urbanlab/Maison-Miniature/CAHIER DE PLANS/MOBILIER/IMPRESSION 3D/SDB-Baignoire.stl

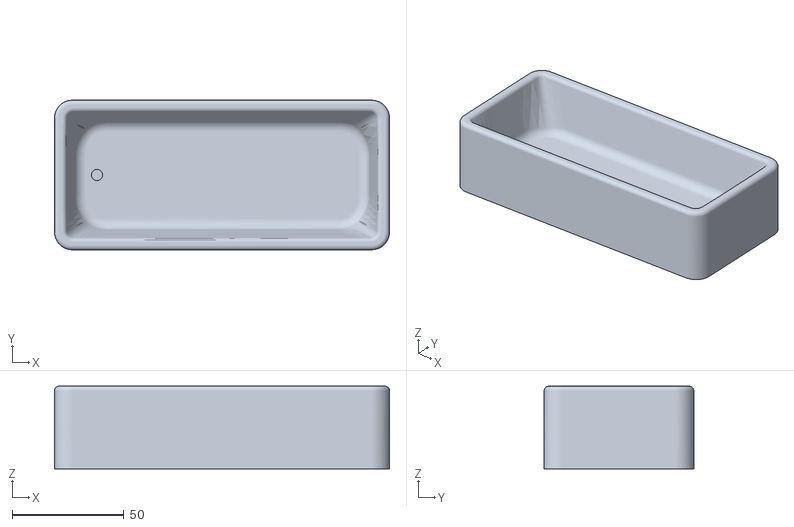
[picture p19: CAD file, 2018-12-10]
CAHIER DE PLANS/MOBILIER/IMPRESSION 3D/SDB-Baignoire.stl
150.0 x 67.0 x 37.0
