urbanlab/Maison-Miniature/CAHIER DE PLANS/MOBILIER/IMPRESSION 3D/SAL-Plafonnier support X2.stl

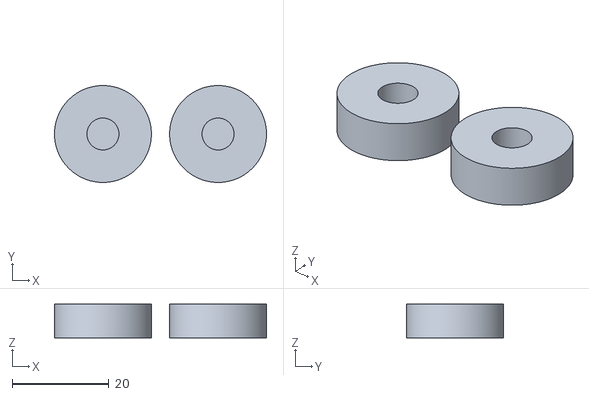
[picture p20: CAD file, 2018-12-10]
CAHIER DE PLANS/MOBILIER/IMPRESSION 3D/SAL-Plafonnier support X2.stl
43.8 x 20.0 x 7.00
