urbanlab/Maison-Miniature/CAHIER DE PLANS/MOBILIER/IMPRESSION 3D/CUIS-Four.stl

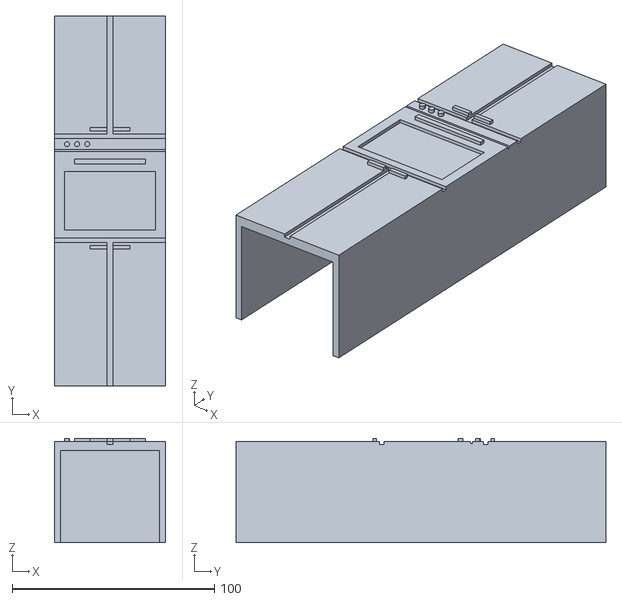
[picture p21: CAD file, 2018-12-10]
CAHIER DE PLANS/MOBILIER/IMPRESSION 3D/CUIS-Four.stl
55.0 x 183.0 x 51.5
