urbanlab/Maison-Miniature/CAHIER DE PLANS/MOBILIER/IMPRESSION 3D/CUIS-Frigo.stl

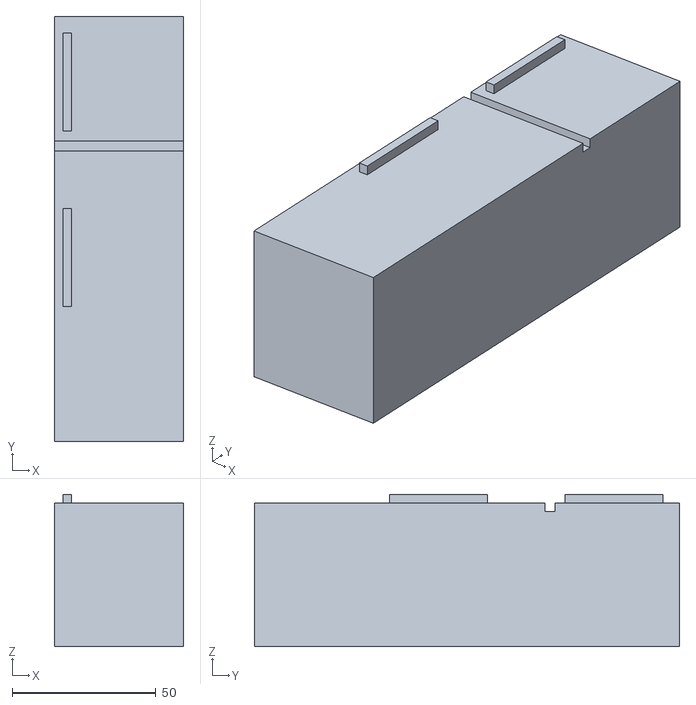
[picture p22: CAD file, 2018-12-10]
CAHIER DE PLANS/MOBILIER/IMPRESSION 3D/CUIS-Frigo.stl
45.0 x 148.0 x 53.0
