urbanlab/Maison-Miniature/CAHIER DE PLANS/MOBILIER/IMPRESSION 3D/SAL-Lampe basse.stl

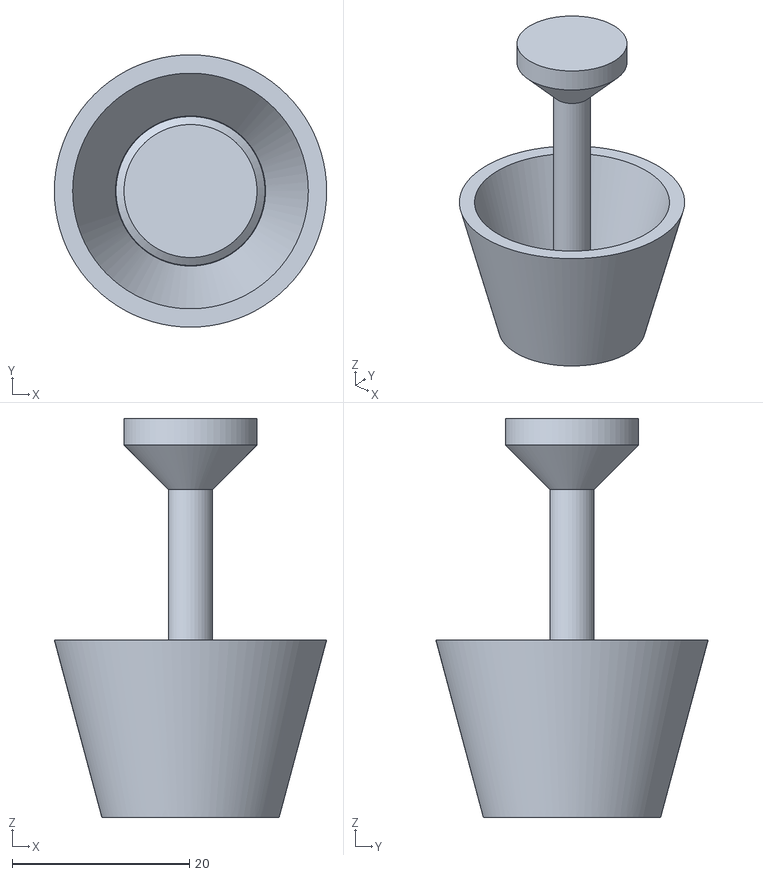
[picture p23: CAD file, 2018-12-10]
CAHIER DE PLANS/MOBILIER/IMPRESSION 3D/SAL-Lampe basse.stl
30.7 x 30.7 x 45.0
