urbanlab/Maison-Miniature/CAHIER DE PLANS/MOBILIER/IMPRESSION 3D/OUV_Porte cuisine.stl

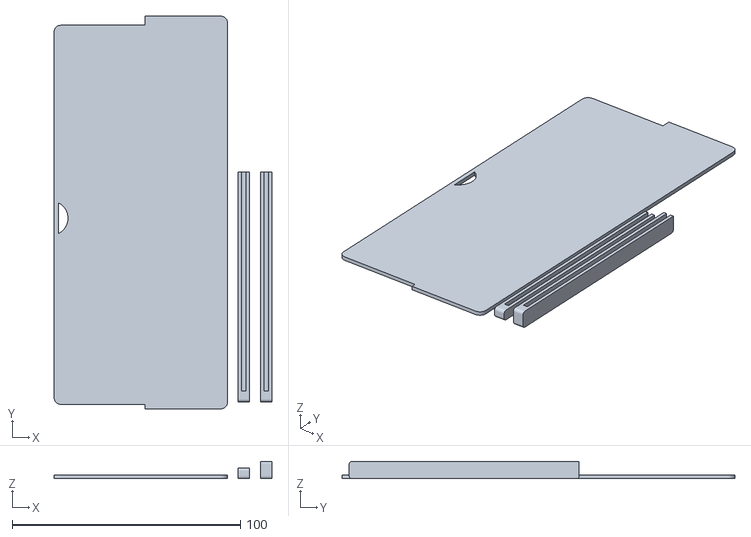
[picture p24: CAD file, 2018-12-10]
CAHIER DE PLANS/MOBILIER/IMPRESSION 3D/OUV_Porte cuisine.stl
95.4 x 172.0 x 7.60
