urbanlab/Maison-Miniature/CAHIER DE PLANS/MOBILIER/IMPRESSION 3D/CUIS-Chaise accoudoire X2.stl

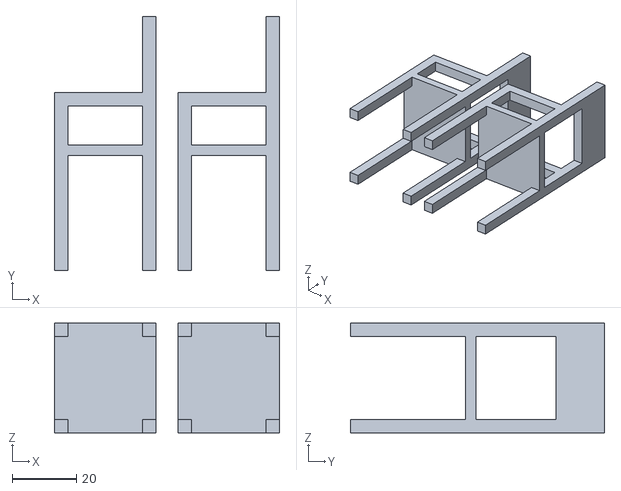
[picture p25: CAD file, 2018-12-10]
CAHIER DE PLANS/MOBILIER/IMPRESSION 3D/CUIS-Chaise accoudoire X2.stl
70.1 x 79.2 x 34.2
