urbanlab/Maison-Miniature/CAHIER DE PLANS/MOBILIER/IMPRESSION 3D/SAL-Fauteuil rehausse.stl

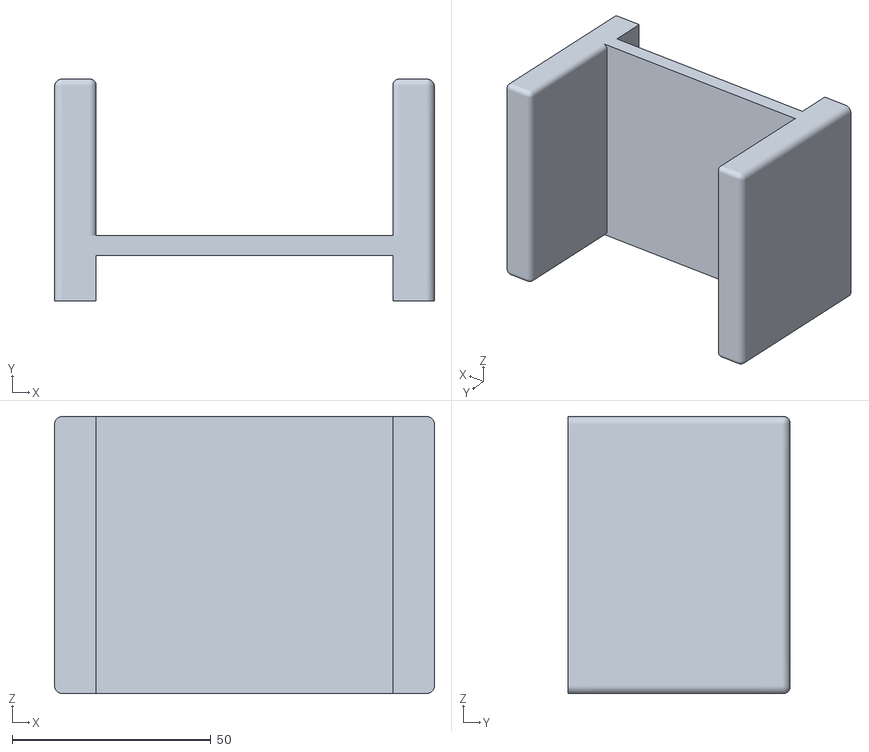
[picture p26: CAD file, 2018-12-10]
CAHIER DE PLANS/MOBILIER/IMPRESSION 3D/SAL-Fauteuil rehausse.stl
95.6 x 55.9 x 69.7
