urbanlab/Maison-Miniature/CAHIER DE PLANS/MOBILIER/IMPRESSION 3D/CUIS-Bloc Vitro.stl

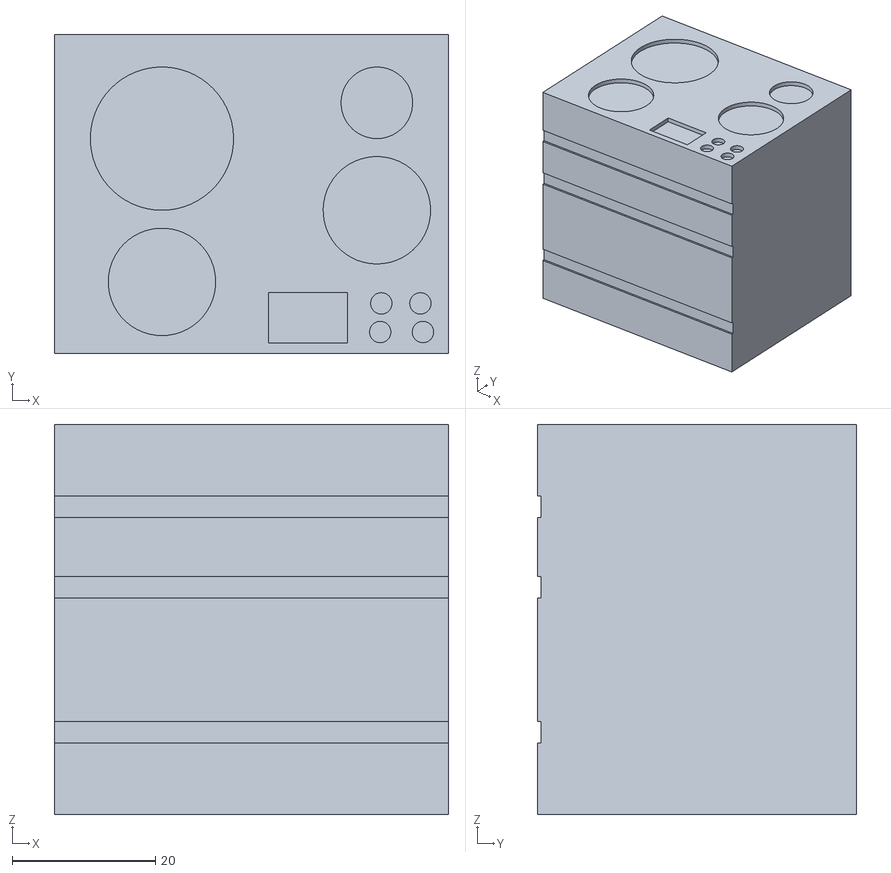
[picture p27: CAD file, 2018-12-10]
CAHIER DE PLANS/MOBILIER/IMPRESSION 3D/CUIS-Bloc Vitro.stl
55.0 x 44.5 x 54.5
