urbanlab/Maison-Miniature/CAHIER DE PLANS/MOBILIER/IMPRESSION 3D/SDB-Lavabo.stl

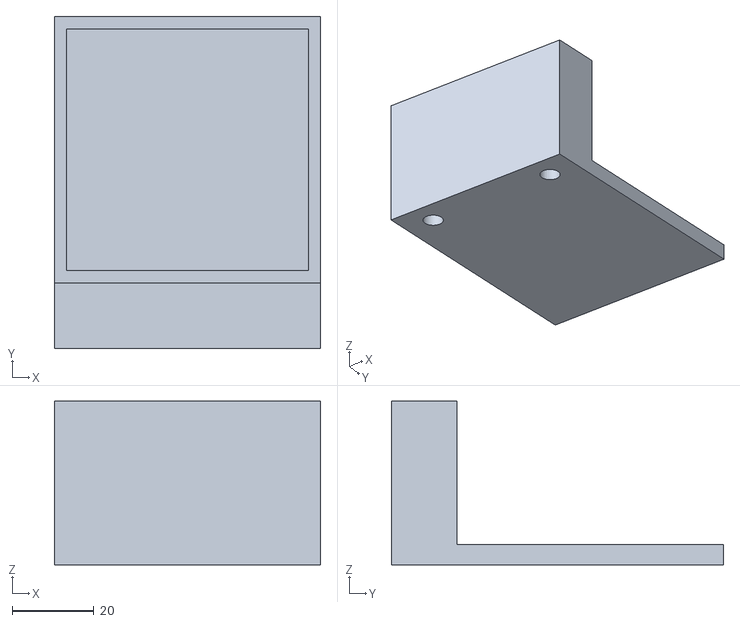
[picture p28: CAD file, 2018-12-10]
CAHIER DE PLANS/MOBILIER/IMPRESSION 3D/SDB-Lavabo.stl
65.0 x 81.0 x 40.0
