urbanlab/Maison-Miniature/CAHIER DE PLANS/MOBILIER/IMPRESSION 3D/CHBRE-Lampe haute.stl

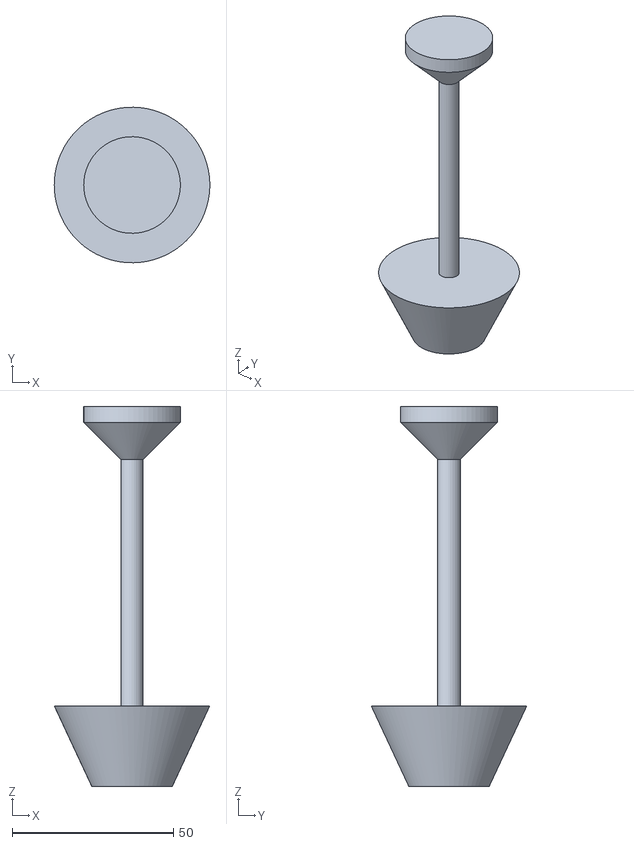
[picture p29: CAD file, 2018-12-10]
CAHIER DE PLANS/MOBILIER/IMPRESSION 3D/CHBRE-Lampe haute.stl
48.3 x 48.3 x 118.0
