urbanlab/Maison-Miniature/CAHIER DE PLANS/MOBILIER/IMPRESSION 3D/SDB-Säche linge.stl

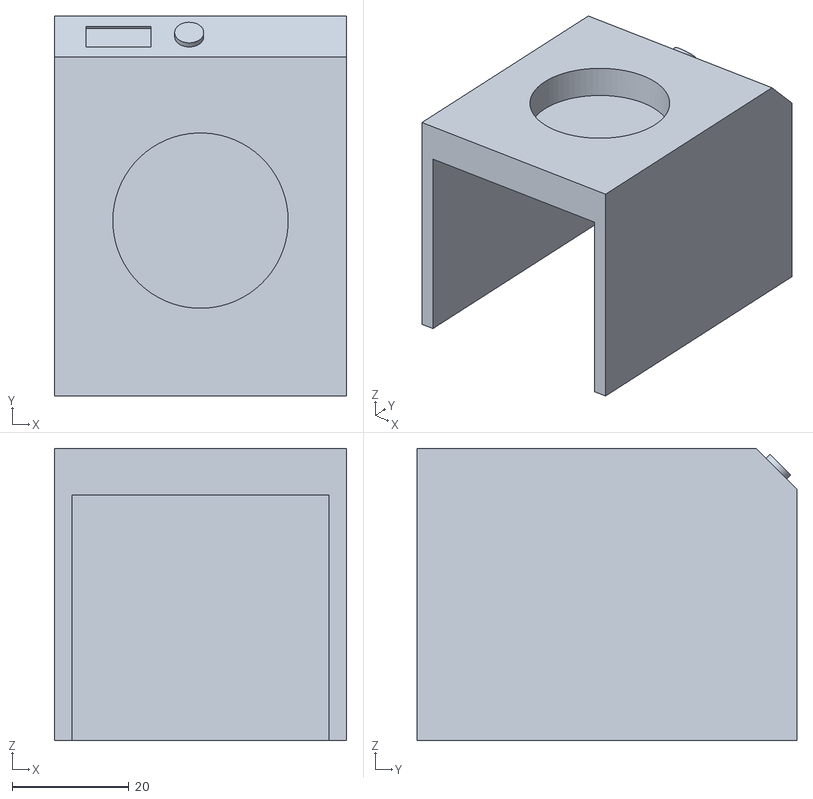
[picture p30: CAD file, 2018-12-10]
CAHIER DE PLANS/MOBILIER/IMPRESSION 3D/SDB-Säche linge.stl
50.0 x 65.0 x 50.0
