urbanlab/Maison-Miniature/CAHIER DE PLANS/MOBILIER/IMPRESSION 3D/SDB-Douche siäge.stl

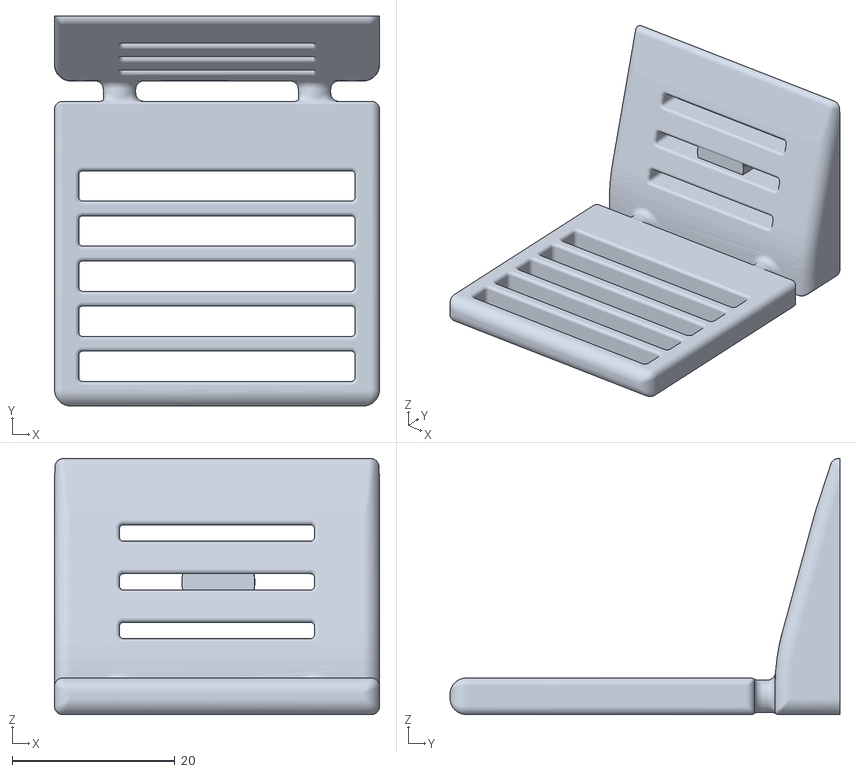
[picture p31: CAD file, 2018-12-10]
CAHIER DE PLANS/MOBILIER/IMPRESSION 3D/SDB-Douche siäge.stl
40.0 x 48.0 x 31.5
