urbanlab/Maison-Miniature/CAHIER DE PLANS/MOBILIER/IMPRESSION 3D/ATR-Pot plante.stl

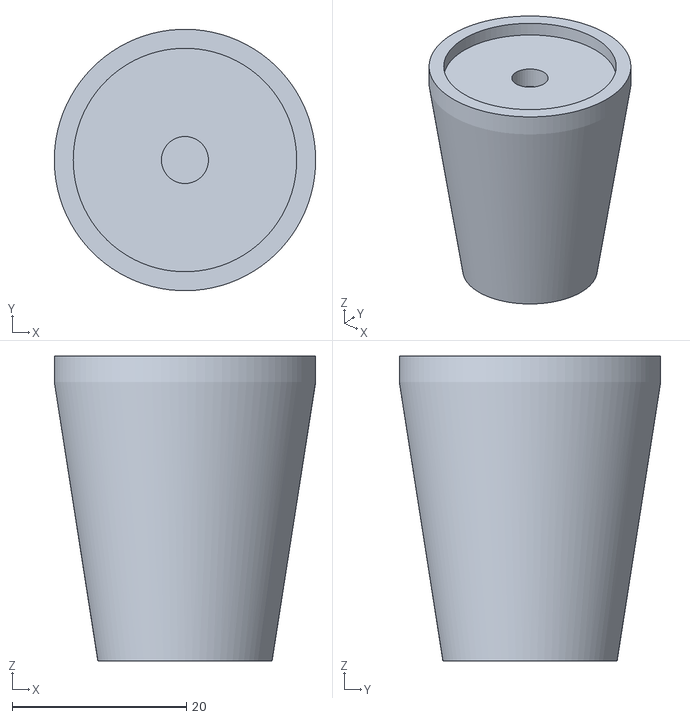
[picture p32: CAD file, 2018-12-10]
CAHIER DE PLANS/MOBILIER/IMPRESSION 3D/ATR-Pot plante.stl
30.0 x 30.0 x 35.0
