urbanlab/Maison-Miniature/CAHIER DE PLANS/MOBILIER/IMPRESSION 3D/ESC_Palier Escalier.stl

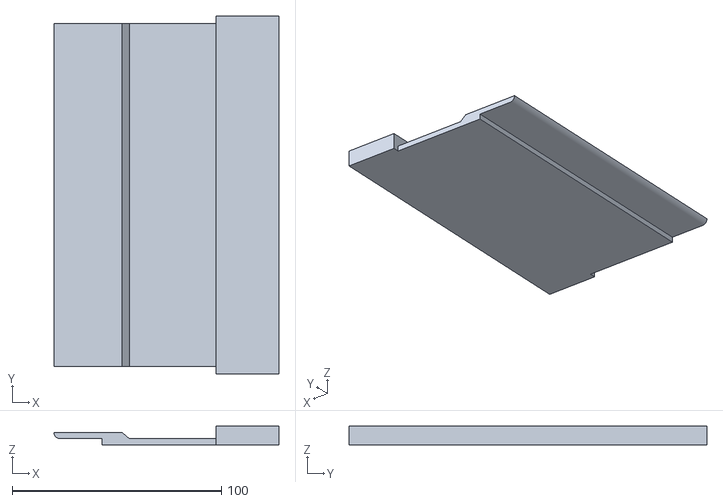
[picture p34: CAD file, 2018-12-10]
CAHIER DE PLANS/MOBILIER/IMPRESSION 3D/ESC_Palier Escalier.stl
107.5 x 171.0 x 9.00
