urbanlab/Maison-Miniature/CAHIER DE PLANS/MOBILIER/IMPRESSION 3D/SDB-Siege baignoire.stl

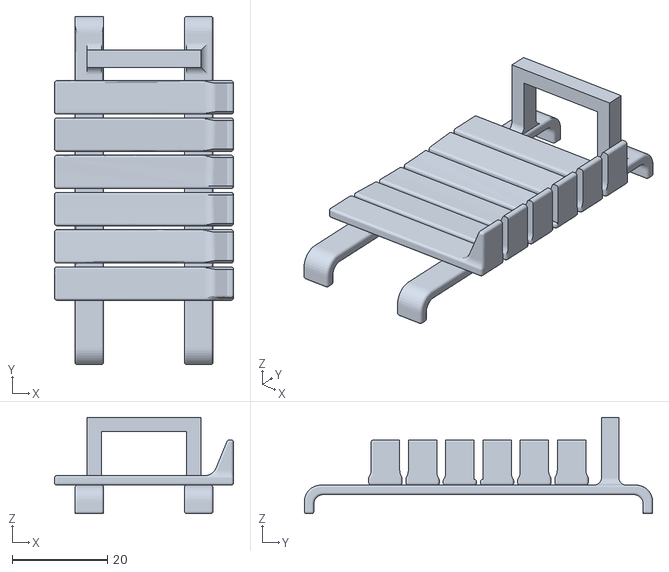
[picture p35: CAD file, 2018-12-10]
CAHIER DE PLANS/MOBILIER/IMPRESSION 3D/SDB-Siege baignoire.stl
37.5 x 73.0 x 20.2
