urbanlab/Maison-Miniature/CAHIER DE PLANS/MOBILIER/IMPRESSION 3D/OUV_Porte SDB.stl

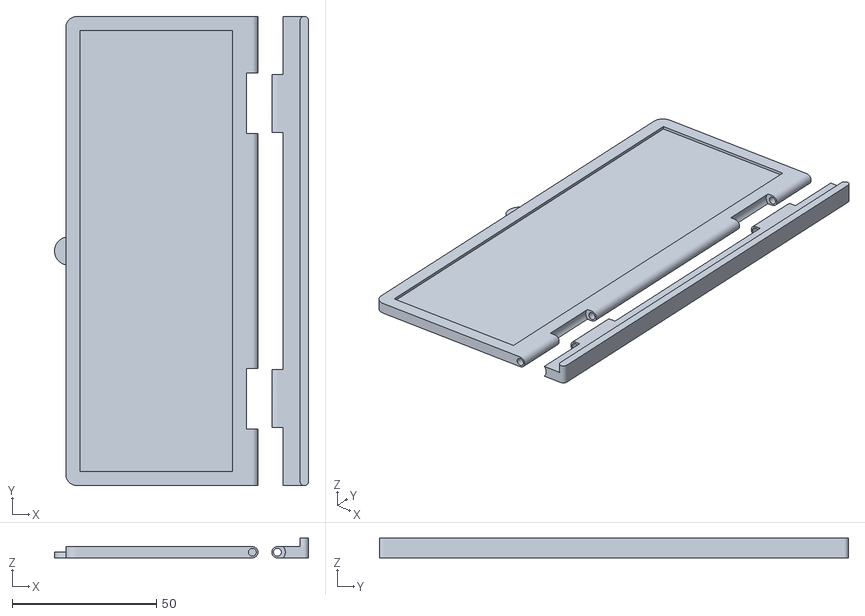
[picture p37: CAD file, 2018-12-10]
CAHIER DE PLANS/MOBILIER/IMPRESSION 3D/OUV_Porte SDB.stl
88.1 x 162.7 x 6.86
