urbanlab/Maison-Miniature/CAHIER DE PLANS/MOBILIER/IMPRESSION 3D/TER-Transat X2.stl

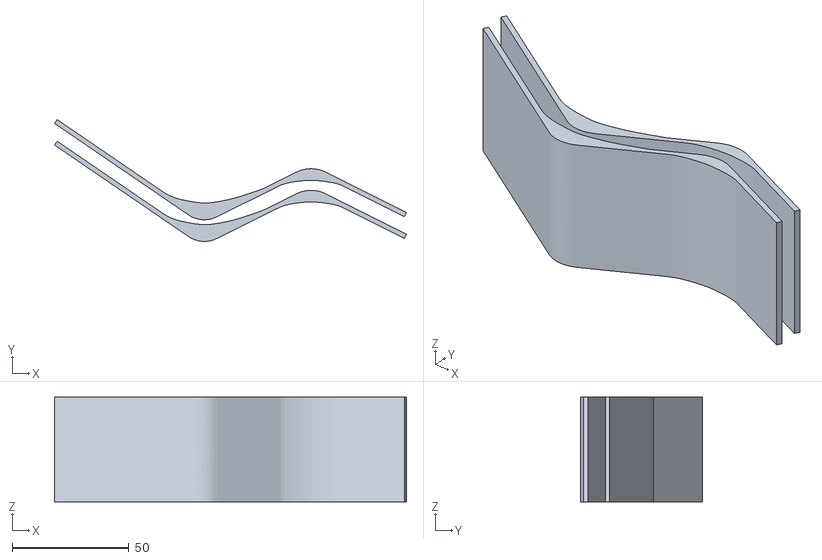
[picture p38: CAD file, 2018-12-10]
CAHIER DE PLANS/MOBILIER/IMPRESSION 3D/TER-Transat X2.stl
150.9 x 52.3 x 45.0
