urbanlab/Maison-Miniature/CAHIER DE PLANS/MOBILIER/IMPRESSION 3D/OUV_Volets chambre.stl

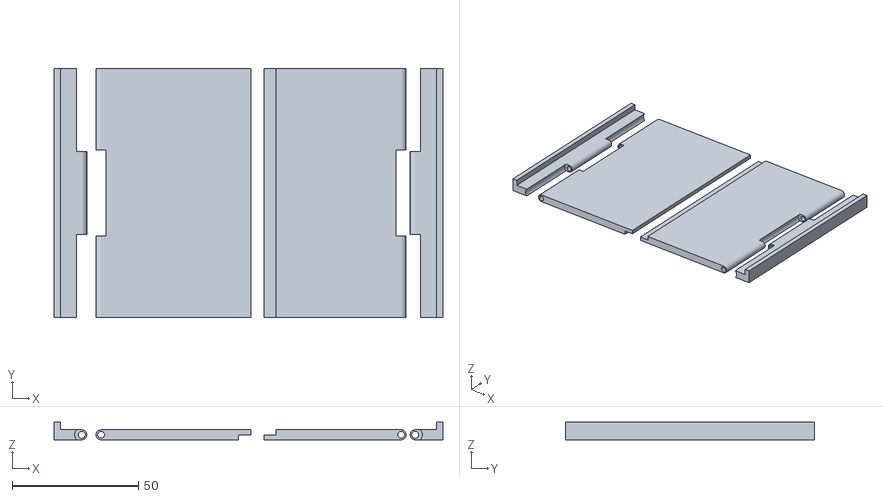
[picture p39: CAD file, 2018-12-10]
CAHIER DE PLANS/MOBILIER/IMPRESSION 3D/OUV_Volets chambre.stl
154.0 x 98.6 x 7.00
