urbanlab/Maison-Miniature/CAHIER DE PLANS/MOBILIER/IMPRESSION 3D/CHBRE-Table chevet X2.stl

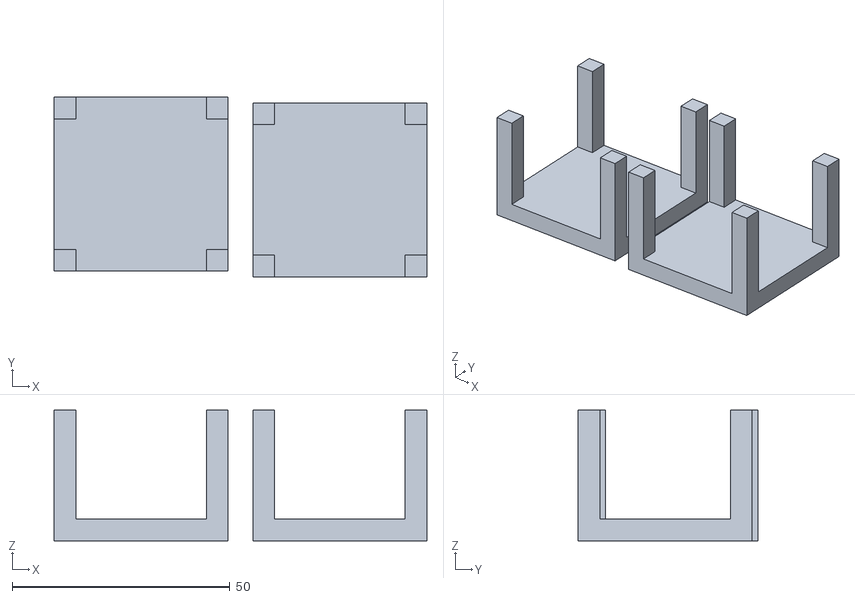
[picture p41: CAD file, 2018-12-10]
CAHIER DE PLANS/MOBILIER/IMPRESSION 3D/CHBRE-Table chevet X2.stl
85.7 x 41.3 x 30.0
