urbanlab/Maison-Miniature/CAHIER DE PLANS/MOBILIER/IMPRESSION 3D/CUIS-Plan de travail Çvier.stl

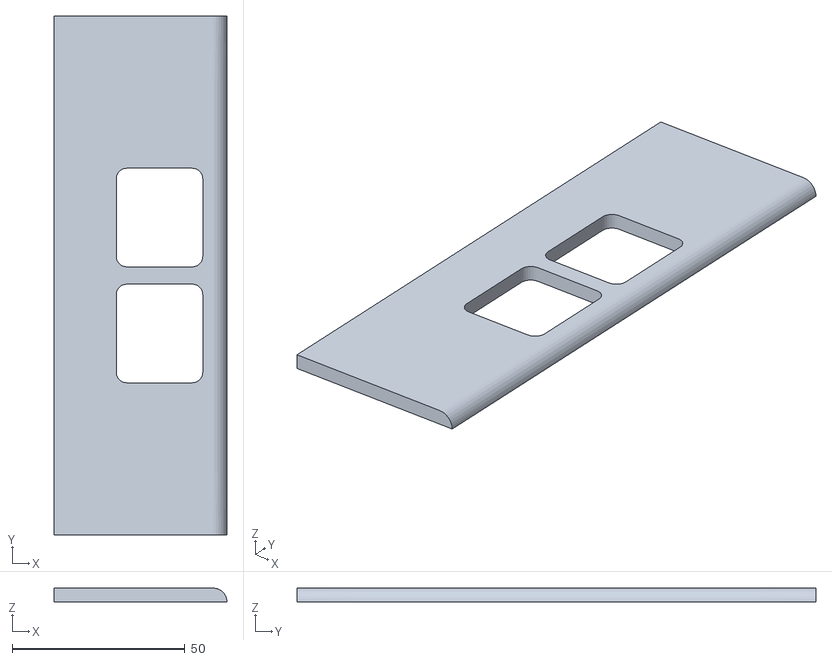
[picture p42: CAD file, 2018-12-10]
CAHIER DE PLANS/MOBILIER/IMPRESSION 3D/CUIS-Plan de travail Çvier.stl
50.0 x 150.0 x 4.00
