urbanlab/Maison-Miniature/CAHIER DE PLANS/MOBILIER/IMPRESSION 3D/SAL-TV.stl

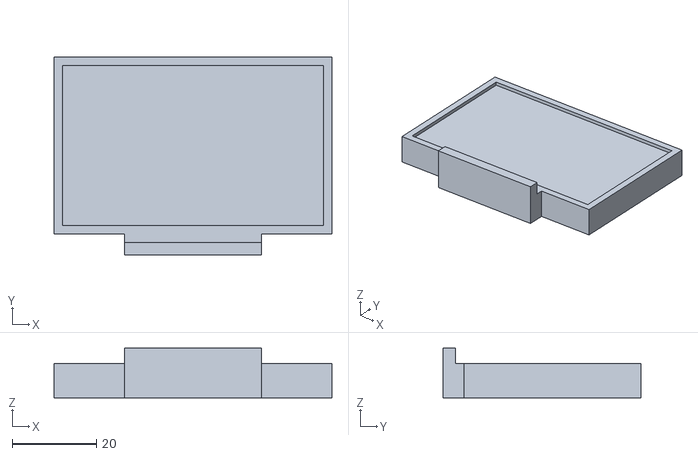
[picture p43: CAD file, 2018-12-10]
CAHIER DE PLANS/MOBILIER/IMPRESSION 3D/SAL-TV.stl
66.0 x 47.0 x 11.8
