urbanlab/Maison-Miniature/CAHIER DE PLANS/MOBILIER/IMPRESSION 3D/CUIS-Plan travail cuisson.stl

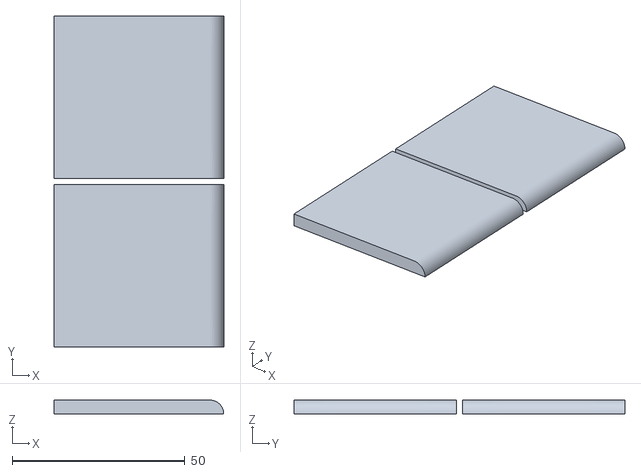
[picture p44: CAD file, 2018-12-10]
CAHIER DE PLANS/MOBILIER/IMPRESSION 3D/CUIS-Plan travail cuisson.stl
49.0 x 95.7 x 4.00
