urbanlab/Maison-Miniature/CAHIER DE PLANS/MOBILIER/IMPRESSION 3D/ATR-Plante.stl

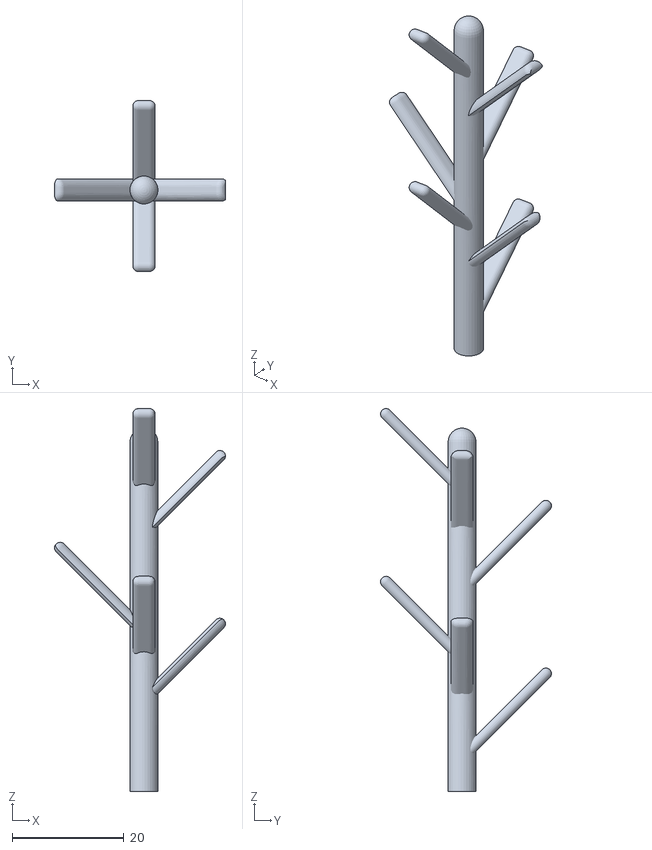
[picture p45: CAD file, 2018-12-10]
CAHIER DE PLANS/MOBILIER/IMPRESSION 3D/ATR-Plante.stl
30.6 x 30.6 x 68.5
