urbanlab/Maison-Miniature/CAHIER DE PLANS/MOBILIER/IMPRESSION 3D/OUV_Store salon.stl

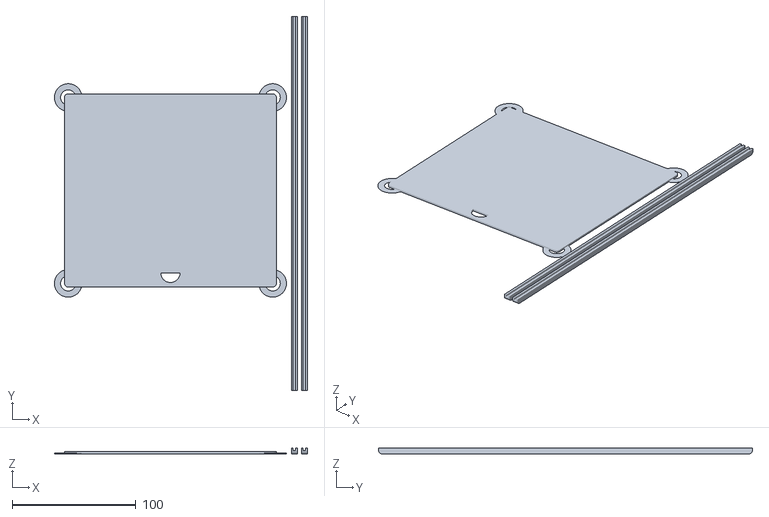
[picture p46: CAD file, 2018-12-10]
CAHIER DE PLANS/MOBILIER/IMPRESSION 3D/OUV_Store salon.stl
204.3 x 301.8 x 4.60
