urbanlab/Maison-Miniature/CAHIER DE PLANS/MOBILIER/IMPRESSION 3D/ESC-VolÇe B.stl

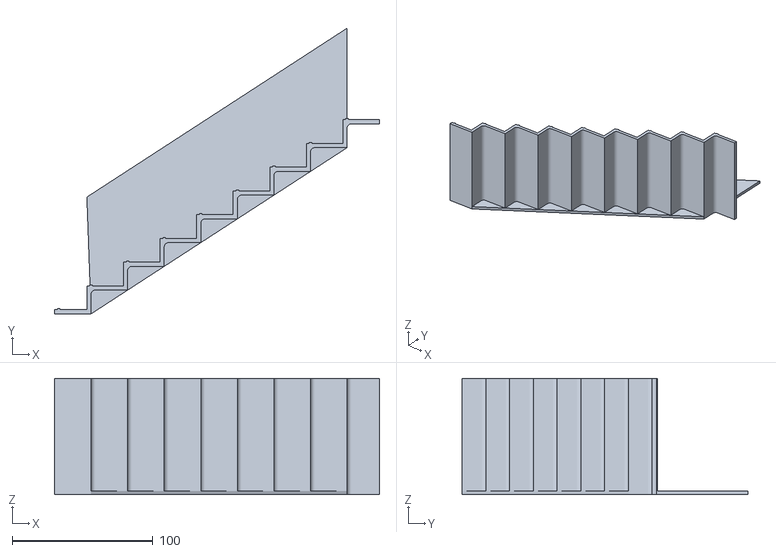
[picture p48: CAD file, 2018-12-10]
CAHIER DE PLANS/MOBILIER/IMPRESSION 3D/ESC-VolÇe B.stl
231.0 x 203.1 x 82.5
