urbanlab/Maison-Miniature/CAHIER DE PLANS/MOBILIER/IMPRESSION 3D/ESC_Palier Escalier X2.stl

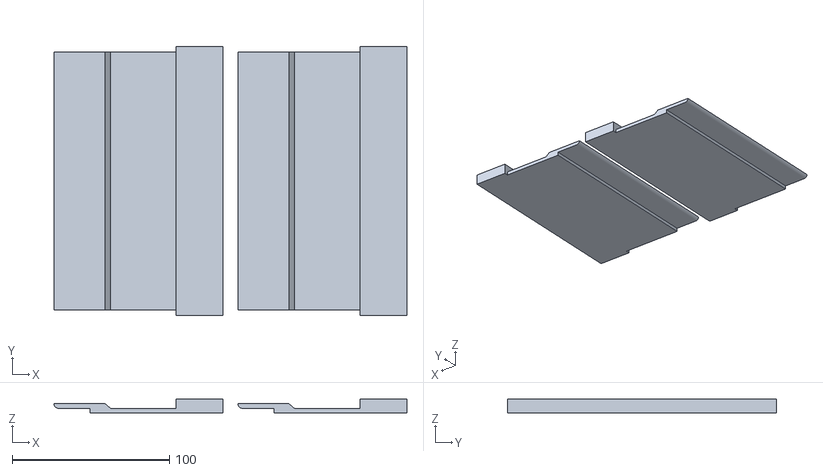
[picture p49: CAD file, 2018-12-10]
CAHIER DE PLANS/MOBILIER/IMPRESSION 3D/ESC_Palier Escalier X2.stl
224.3 x 171.0 x 9.00
