urbanlab/Maison-Miniature/CAHIER DE PLANS/MOBILIER/IMPRESSION 3D/TER-Table exterieur.stl

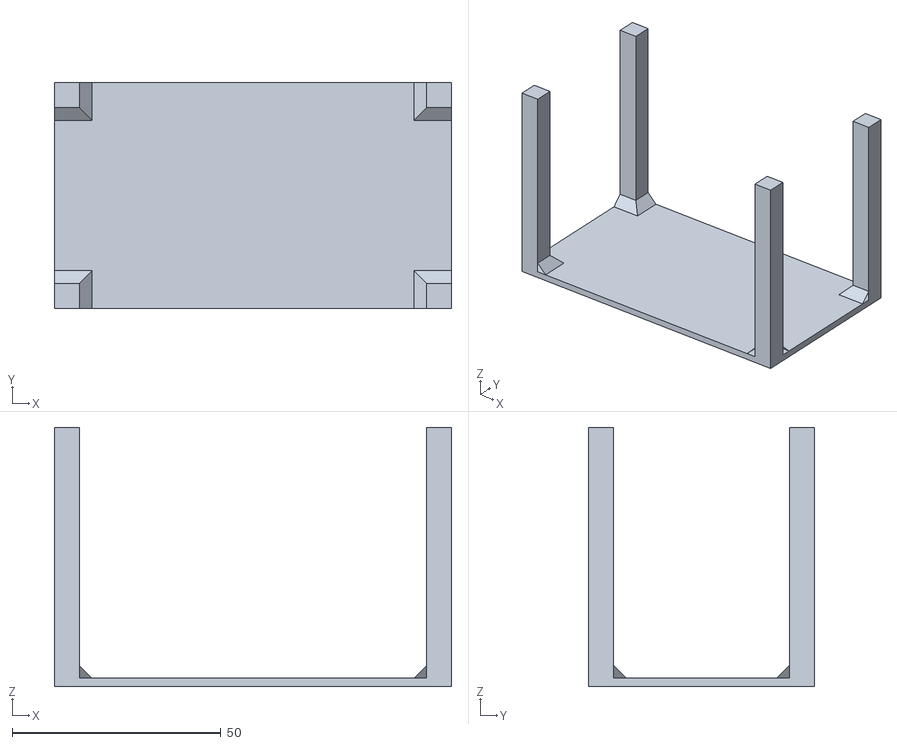
[picture p50: CAD file, 2018-12-10]
CAHIER DE PLANS/MOBILIER/IMPRESSION 3D/TER-Table exterieur.stl
95.0 x 54.0 x 62.0
