urbanlab/Maison-Miniature/CAHIER DE PLANS/MOBILIER/IMPRESSION 3D/CUIS-Bloc gaziniäre.stl

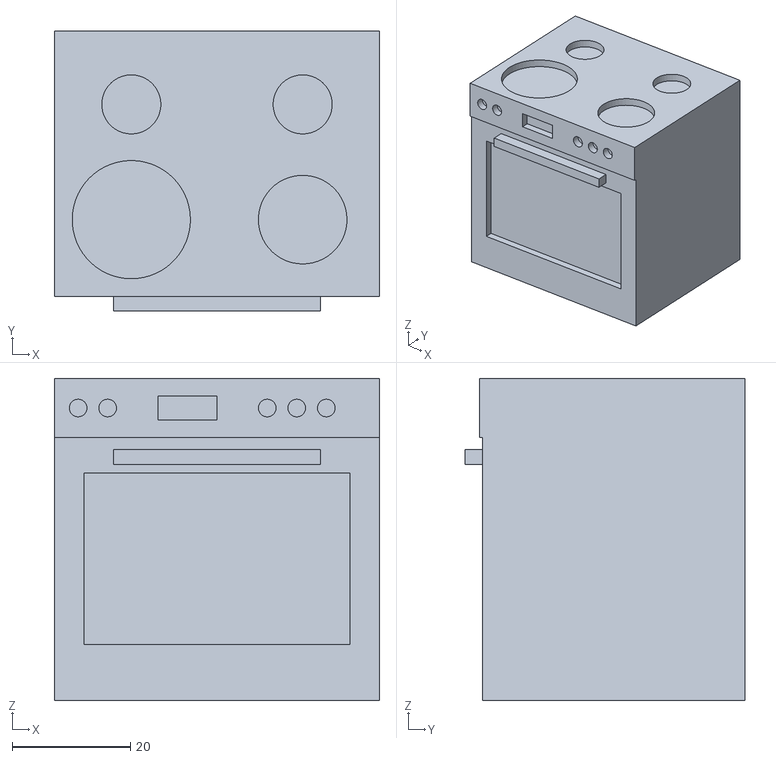
[picture p51: CAD file, 2018-12-10]
CAHIER DE PLANS/MOBILIER/IMPRESSION 3D/CUIS-Bloc gaziniäre.stl
55.0 x 47.5 x 54.5
