urbanlab/Maison-Miniature/CAHIER DE PLANS/MOBILIER/IMPRESSION 3D/TER-Rampes.stl

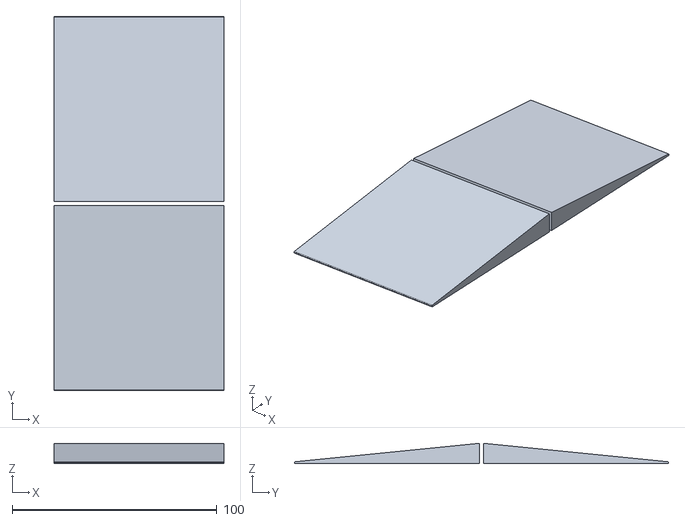
[picture p52: CAD file, 2018-12-10]
CAHIER DE PLANS/MOBILIER/IMPRESSION 3D/TER-Rampes.stl
83.0 x 182.8 x 10.0
