urbanlab/Maison-Miniature/CAHIER DE PLANS/MOBILIER/IMPRESSION 3D/ATR-Cartons.stl

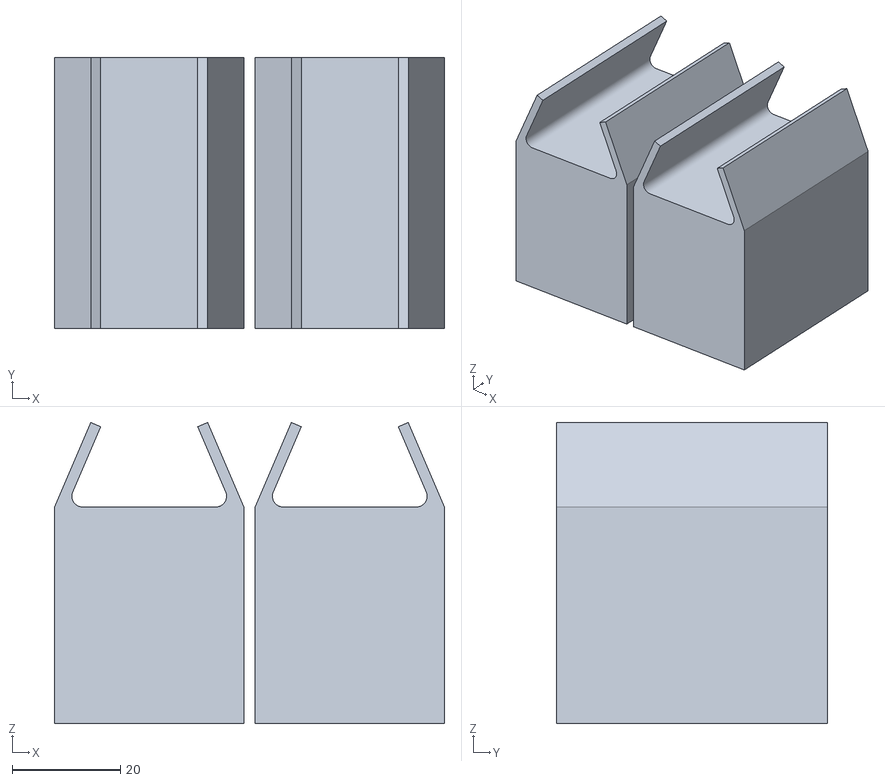
[picture p53: CAD file, 2018-12-10]
CAHIER DE PLANS/MOBILIER/IMPRESSION 3D/ATR-Cartons.stl
72.1 x 50.0 x 55.6
