urbanlab/Maison-Miniature/CAHIER DE PLANS/MOBILIER/IMPRESSION 3D/CHBRE-Matelas.stl

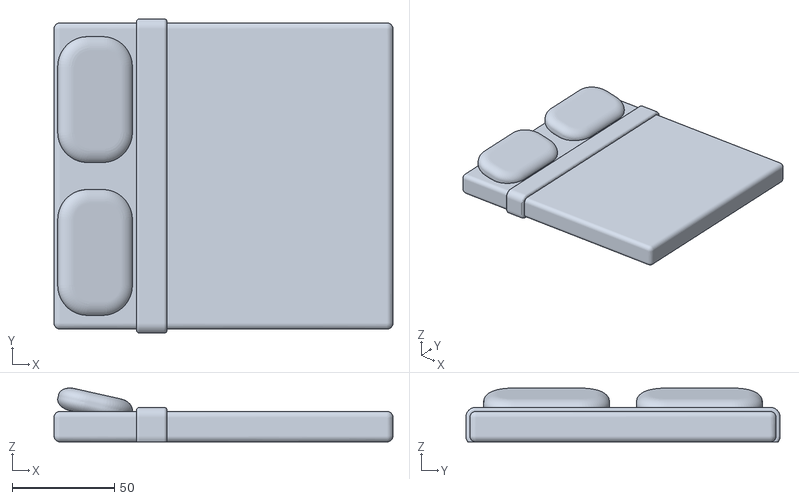
[picture p55: CAD file, 2018-12-10]
CAHIER DE PLANS/MOBILIER/IMPRESSION 3D/CHBRE-Matelas.stl
166.0 x 154.0 x 26.4
