urbanlab/Maison-Miniature/CAHIER DE PLANS/MOBILIER/IMPRESSION 3D/CHBRE-Sommier.stl

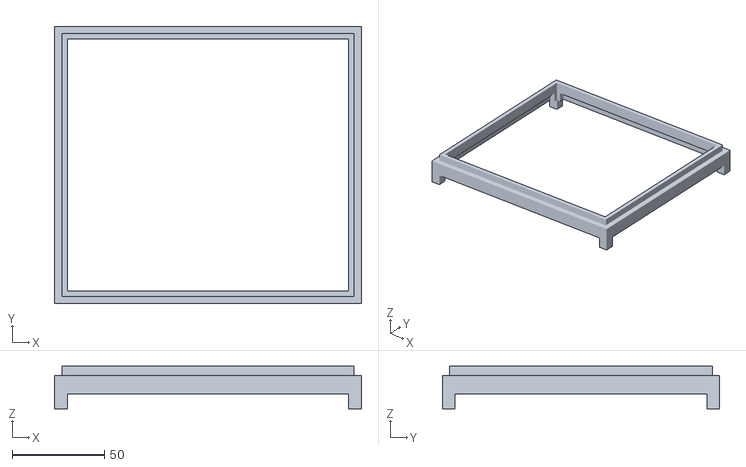
[picture p57: CAD file, 2018-12-10]
CAHIER DE PLANS/MOBILIER/IMPRESSION 3D/CHBRE-Sommier.stl
166.0 x 150.0 x 23.0
