urbanlab/Maison-Miniature/CAHIER DE PLANS/MOBILIER/IMPRESSION 3D/SAL-Canape rehausse.stl

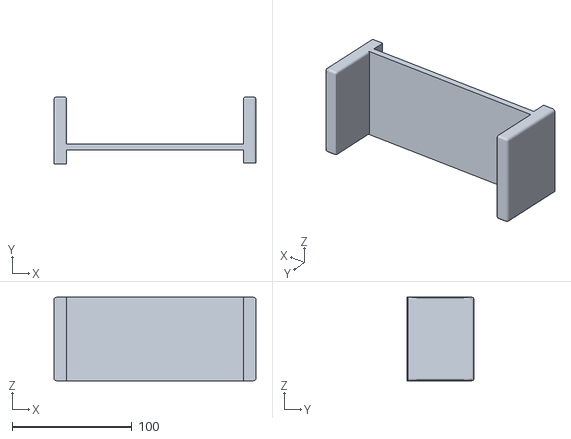
[picture p60: CAD file, 2018-12-10]
CAHIER DE PLANS/MOBILIER/IMPRESSION 3D/SAL-Canape rehausse.stl
168.6 x 55.9 x 69.7
