urbanlab/Maison-Miniature/CAHIER DE PLANS/MOBILIER/IMPRESSION 3D/TER-Plateau table ext.stl

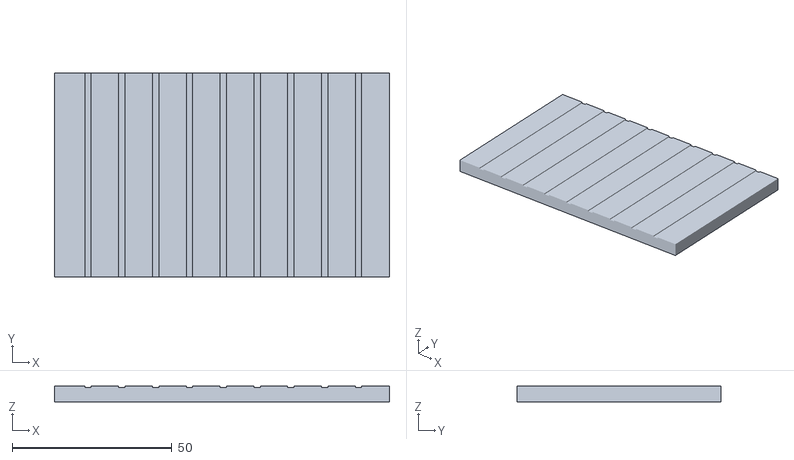
[picture p62: CAD file, 2018-12-10]
CAHIER DE PLANS/MOBILIER/IMPRESSION 3D/TER-Plateau table ext.stl
105.0 x 64.0 x 5.00
